calvin-mcd/universal-vault/Project/hhkb universal.kicad_sch

## KiCad design Project/hhkb universal.kicad_sch (2023-12-22)

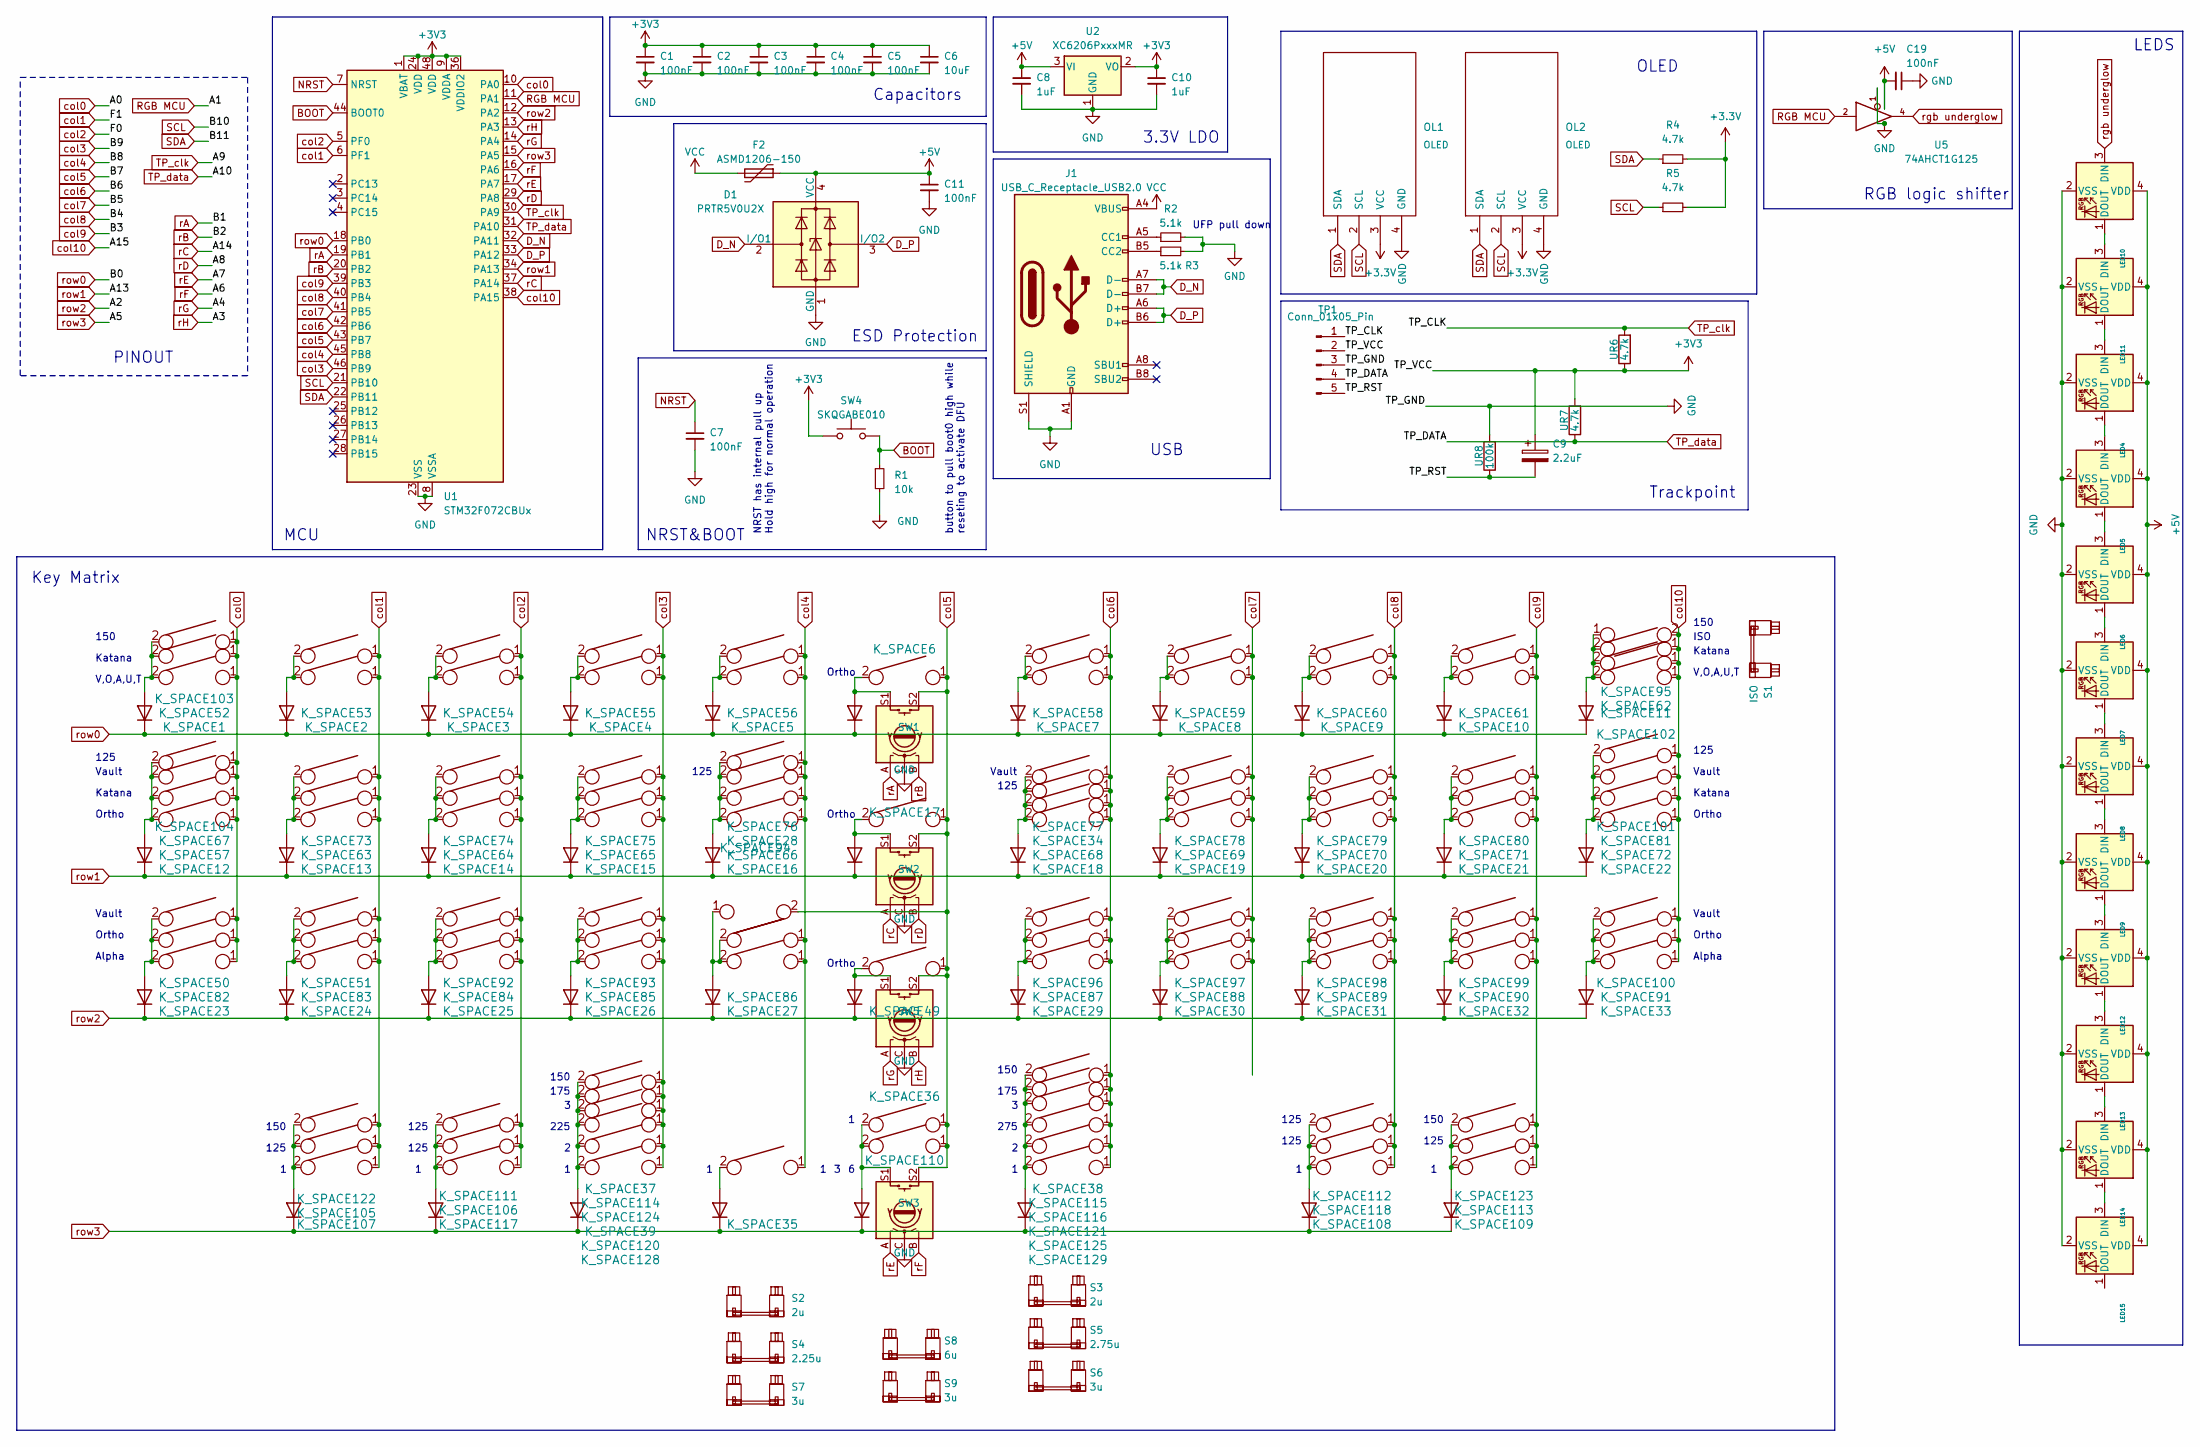
[picture p5: schematic hhkb universal.kicad_sch]

Parts:
C1, C2, C3, C4, C5, C7, C11, C19: 100nF; C_0402_1005Metric; LCSC C1525
C6: 10uF; C_0402_1005Metric; LCSC C315248
C8, C10: 1uF; C_0402_1005Metric; LCSC C14445
C9: 2.2uF; C_0805_2012Metric
D1: PRTR5V0U2X; SOT-143; LCSC C2827688
D_SPACE1, D_SPACE2, D_SPACE3, D_SPACE4, D_SPACE5, D_SPACE6, D_SPACE7, D_SPACE8, D_SPACE9, D_SPACE10, D_SPACE11, D_SPACE12, D_SPACE13, D_SPACE14, D_SPACE15, D_SPACE16, D_SPACE17, D_SPACE18, D_SPACE19, D_SPACE20, D_SPACE21, D_SPACE22, D_SPACE23, D_SPACE24, D_SPACE25, D_SPACE26, D_SPACE27, D_SPACE28, D_SPACE29, D_SPACE30, D_SPACE31, D_SPACE32, D_SPACE33, D_SPACE34, D_SPACE35, D_SPACE36, D_SPACE37, D_SPACE38, D_SPACE39, D_SPACE40, D_SPACE42: D; D_SOD-123F; LCSC C81598
F2: ASMD1206-150; Fuse_1206_3216Metric; LCSC C135341
J1: USB_C_Receptacle_USB2.0; USB_C_Receptacle_HRO_TYPE-C-31-M-12; JlcRotOffset 180
K_SPACE1, K_SPACE2, K_SPACE3, K_SPACE4, K_SPACE5, K_SPACE6, K_SPACE7, K_SPACE8, K_SPACE9, K_SPACE10, K_SPACE11, K_SPACE12, K_SPACE13, K_SPACE14, K_SPACE15, K_SPACE16, K_SPACE17, K_SPACE18, K_SPACE19, K_SPACE20, K_SPACE21, K_SPACE22, K_SPACE24, K_SPACE25, K_SPACE26, K_SPACE27, K_SPACE29, K_SPACE30, K_SPACE31, K_SPACE32, K_SPACE35, K_SPACE36, K_SPACE39, K_SPACE49, K_SPACE51, K_SPACE52, K_SPACE53, K_SPACE54, K_SPACE55, K_SPACE56, K_SPACE57, K_SPACE58, K_SPACE59, K_SPACE60, K_SPACE61, K_SPACE62, K_SPACE63, K_SPACE64, K_SPACE65, K_SPACE66, K_SPACE68, K_SPACE69, K_SPACE70, K_SPACE71, K_SPACE72, K_SPACE73, K_SPACE74, K_SPACE75, K_SPACE76, K_SPACE77, K_SPACE78, K_SPACE79, K_SPACE80, K_SPACE82, K_SPACE83, K_SPACE84, K_SPACE85, K_SPACE86, K_SPACE87, K_SPACE88, K_SPACE89, K_SPACE90, K_SPACE91, K_SPACE92, K_SPACE93, K_SPACE94, K_SPACE95, K_SPACE96, K_SPACE97, K_SPACE98, K_SPACE99, K_SPACE105, K_SPACE110, K_SPACE113, K_SPACE116, K_SPACE117, K_SPACE118, K_SPACE120, K_SPACE121, K_SPACE124, K_SPACE125, K_SPACE128, K_SPACE129: KEYSW; SW_MX_1u
K_SPACE23, K_SPACE33, K_SPACE37, K_SPACE38, K_SPACE102, K_SPACE103, K_SPACE122, K_SPACE123: KEYSW; SW_MX_1.5u
K_SPACE28, K_SPACE34, K_SPACE67, K_SPACE100, K_SPACE101, K_SPACE104, K_SPACE106, K_SPACE107, K_SPACE108, K_SPACE109, K_SPACE111, K_SPACE112: KEYSW; SW_MX_1.25u
K_SPACE50, K_SPACE81, K_SPACE114, K_SPACE115: KEYSW; SW_MX_1.75u
LED4, LED5, LED6, LED7, LED8, LED9, LED10, LED11, LED12, LED13, LED14, LED15: WS2812_2020; LED_WS2812_2020; LCSC C965555
OL1, OL2: OLED; OLED_v2
R1: 10k; R_0402_1005Metric; LCSC C25744
R2, R3: 5.1k; R_0402_1005Metric; LCSC C25905
R4, R5: 4.7k; R_0402_1005Metric; LCSC C25900
S1: ISO; STAB_MX_ISO
S2, S3: 2u; STAB_MX_2u
S4: 2.25u; STAB_MX_2.25u
S5: 2.75u; STAB_MX_2.75u
S6, S7, S9: 3u; STAB_MX_3u
S8: 6u; STAB_MX_6u
SW1, SW2, SW3, SW5: RotaryEncoder_Switch; ROT_Alps_EC11E-Switch
SW4: SKQGABE010; SW_SPST_SKQG_WithStem; LCSC C115351
TP1: Conn_01x05_Pin; PinSocket_1x05_P2.00mm_Vertical
U1: STM32F072CBUx; QFN-48-1EP_7x7mm_P0.5mm_EP5.6x5.6mm; LCSC C92504
U2: XC6206PxxxMR; SOT-23-3; LCSC C5446
U5: 74AHCT1G125; TSOT-23-5; LCSC C12494
UR6, UR7: 4.7k; R_0805_2012Metric_Pad1.20x1.40mm_HandSolder
UR8: 100k; R_0805_2012Metric_Pad1.20x1.40mm_HandSolder

Connections:
+3.3V: OL1.3 (VCC), OL2.3 (VCC), R4.2, R5.2
+3V3: C1.1, C2.1, C3.1, C4.1, C5.1, C6.1, C9.1, C10.1, SW4.1, TP1.2, U1.1 (VBAT), U1.9 (VDDA), U1.24 (VDD), U1.36 (VDDIO2), U1.48 (VDD), U2.2 (VO), UR6.1, UR7.2
+5V: C8.1, C11.1, C19.2, D1.4 (VCC), F2.1, LED4.4 (VDD), LED5.4 (VDD), LED6.4 (VDD), LED7.4 (VDD), LED8.4 (VDD), LED9.4 (VDD), LED10.4 (VDD), LED11.4 (VDD), LED12.4 (VDD), LED13.4 (VDD), LED14.4 (VDD), LED15.4 (VDD), U2.3 (VI), U5.5 (+5V)
BOOT: R1.1, SW4.2, U1.44 (BOOT0)
D_N: D1.2 (I/O1), J1.A7 (D-), J1.B7 (D-), U1.32 (PA11)
D_P: D1.3 (I/O2), J1.A6 (D+), J1.B6 (D+), U1.33 (PA12)
GND: C1.2, C2.2, C3.2, C4.2, C5.2, C6.2, C7.2, C8.2, C10.2, C11.2, C19.1, D1.1 (GND), J1.A1 (GND), J1.A12 (GND), J1.B1 (GND), J1.B12 (GND), J1.S1 (SHIELD), LED4.2 (VSS), LED5.2 (VSS), LED6.2 (VSS), LED7.2 (VSS), LED8.2 (VSS), LED9.2 (VSS), LED10.2 (VSS), LED11.2 (VSS), LED12.2 (VSS), LED13.2 (VSS), LED14.2 (VSS), LED15.2 (VSS), OL1.4 (GND), OL2.4 (GND), R1.2, R2.2, R3.2, SW1.C, SW2.C, SW3.C, SW5.C, TP1.3, U1.8 (VSSA), U1.23 (VSS), U1.35 (VSS), U1.47 (VSS), U1.49 (VSS), U2.1 (GND), U5.1, U5.3 (GND), UR8.2
NRST: C7.1, U1.7 (NRST)
unnamed: D_SPACE1.2 (A), K_SPACE1.2, K_SPACE52.2, K_SPACE103.2
unnamed: D_SPACE2.2 (A), K_SPACE2.2, K_SPACE53.2
unnamed: D_SPACE3.2 (A), K_SPACE3.2, K_SPACE54.2
unnamed: D_SPACE4.2 (A), K_SPACE4.2, K_SPACE55.2
unnamed: D_SPACE5.2 (A), K_SPACE5.2, K_SPACE56.2
unnamed: D_SPACE6.2 (A), K_SPACE6.2, SW1.S1
unnamed: D_SPACE7.2 (A), K_SPACE7.2, K_SPACE58.2
unnamed: D_SPACE8.2 (A), K_SPACE8.2, K_SPACE59.2
unnamed: D_SPACE9.2 (A), K_SPACE9.2, K_SPACE60.2
unnamed: D_SPACE10.2 (A), K_SPACE10.2, K_SPACE61.2
unnamed: D_SPACE11.2 (A), K_SPACE11.2, K_SPACE62.2, K_SPACE95.2, K_SPACE102.1
unnamed: D_SPACE12.2 (A), K_SPACE12.2, K_SPACE57.2, K_SPACE67.2, K_SPACE104.2
unnamed: D_SPACE13.2 (A), K_SPACE13.2, K_SPACE63.2, K_SPACE73.2
unnamed: D_SPACE14.2 (A), K_SPACE14.2, K_SPACE64.2, K_SPACE74.2
unnamed: D_SPACE15.2 (A), K_SPACE15.2, K_SPACE65.2, K_SPACE75.2
unnamed: D_SPACE16.2 (A), K_SPACE16.2, K_SPACE28.2, K_SPACE66.2, K_SPACE76.2
unnamed: D_SPACE17.2 (A), K_SPACE17.2, SW2.S1
unnamed: D_SPACE18.2 (A), K_SPACE18.2, K_SPACE34.2, K_SPACE68.2, K_SPACE77.2
unnamed: D_SPACE19.2 (A), K_SPACE19.2, K_SPACE69.2, K_SPACE78.2
unnamed: D_SPACE20.2 (A), K_SPACE20.2, K_SPACE70.2, K_SPACE79.2
unnamed: D_SPACE21.2 (A), K_SPACE21.2, K_SPACE71.2, K_SPACE80.2
unnamed: D_SPACE22.2 (A), K_SPACE22.2, K_SPACE72.2, K_SPACE81.2, K_SPACE101.2
unnamed: D_SPACE23.2 (A), K_SPACE23.2, K_SPACE50.2, K_SPACE82.2
unnamed: D_SPACE24.2 (A), K_SPACE24.2, K_SPACE51.2, K_SPACE83.2
unnamed: D_SPACE25.2 (A), K_SPACE25.2, K_SPACE84.2, K_SPACE92.2
unnamed: D_SPACE26.2 (A), K_SPACE26.2, K_SPACE85.2, K_SPACE93.2
unnamed: D_SPACE27.2 (A), K_SPACE27.2, K_SPACE86.2, K_SPACE94.1
unnamed: D_SPACE28.2 (A), K_SPACE49.2, SW5.S1
unnamed: D_SPACE29.2 (A), K_SPACE29.2, K_SPACE87.2, K_SPACE96.2
unnamed: D_SPACE30.2 (A), K_SPACE30.2, K_SPACE88.2, K_SPACE97.2
unnamed: D_SPACE31.2 (A), K_SPACE31.2, K_SPACE89.2, K_SPACE98.2
unnamed: D_SPACE32.2 (A), K_SPACE32.2, K_SPACE90.2, K_SPACE99.2
unnamed: D_SPACE33.2 (A), K_SPACE33.2, K_SPACE91.2, K_SPACE100.2
unnamed: D_SPACE34.2 (A), K_SPACE105.2, K_SPACE107.2, K_SPACE122.2
unnamed: D_SPACE35.2 (A), K_SPACE106.2, K_SPACE111.2, K_SPACE117.2
unnamed: D_SPACE36.2 (A), K_SPACE37.2, K_SPACE39.2, K_SPACE114.2, K_SPACE120.2, K_SPACE124.2, K_SPACE128.2
unnamed: D_SPACE37.2 (A), K_SPACE35.2
unnamed: D_SPACE38.2 (A), K_SPACE38.2, K_SPACE115.2, K_SPACE116.2, K_SPACE121.2, K_SPACE125.2, K_SPACE129.2
unnamed: D_SPACE39.2 (A), K_SPACE108.2, K_SPACE112.2, K_SPACE118.2
unnamed: D_SPACE40.2 (A), K_SPACE109.2, K_SPACE113.2, K_SPACE123.2
unnamed: D_SPACE42.2 (A), K_SPACE36.2, K_SPACE110.2, SW3.S1
unnamed: J1.A5 (CC1), R2.1
unnamed: J1.B5 (CC2), R3.1
unnamed: LED4.1 (DOUT), LED5.3 (DIN)
unnamed: LED5.1 (DOUT), LED6.3 (DIN)
unnamed: LED6.1 (DOUT), LED7.3 (DIN)
unnamed: LED7.1 (DOUT), LED8.3 (DIN)
unnamed: LED8.1 (DOUT), LED9.3 (DIN)
unnamed: LED10.1 (DOUT), LED11.3 (DIN)
unnamed: LED4.3 (DIN), LED11.1 (DOUT)
unnamed: LED12.1 (DOUT), LED13.3 (DIN)
unnamed: LED9.1 (DOUT), LED12.3 (DIN)
unnamed: LED13.1 (DOUT), LED14.3 (DIN)
unnamed: LED14.1 (DOUT), LED15.3 (DIN)
RGB MCU: U1.11 (PA1), U5.2
SCL: OL1.2 (SCL), OL2.2 (SCL), R5.1, U1.21 (PB10)
SDA: OL1.1 (SDA), OL2.1 (SDA), R4.1, U1.22 (PB11)
TP_RST: C9.2, TP1.5, UR8.1
TP_clk: TP1.1, U1.30 (PA9), UR6.2
TP_data: TP1.4, U1.31 (PA10), UR7.1
VCC: F2.2, J1.A4 (VBUS), J1.A9 (VBUS), J1.B4 (VBUS), J1.B9 (VBUS)
col0: K_SPACE1.1, K_SPACE12.1, K_SPACE23.1, K_SPACE50.1, K_SPACE52.1, K_SPACE57.1, K_SPACE67.1, K_SPACE82.1, K_SPACE103.1, K_SPACE104.1, U1.10 (PA0)
col1: K_SPACE2.1, K_SPACE13.1, K_SPACE24.1, K_SPACE51.1, K_SPACE53.1, K_SPACE63.1, K_SPACE73.1, K_SPACE83.1, K_SPACE105.1, K_SPACE107.1, K_SPACE122.1, U1.6 (PF1)
col2: K_SPACE3.1, K_SPACE14.1, K_SPACE25.1, K_SPACE54.1, K_SPACE64.1, K_SPACE74.1, K_SPACE84.1, K_SPACE92.1, K_SPACE106.1, K_SPACE111.1, K_SPACE117.1, U1.5 (PF0)
col3: K_SPACE4.1, K_SPACE15.1, K_SPACE26.1, K_SPACE37.1, K_SPACE39.1, K_SPACE55.1, K_SPACE65.1, K_SPACE75.1, K_SPACE85.1, K_SPACE93.1, K_SPACE114.1, K_SPACE120.1, K_SPACE124.1, K_SPACE128.1, U1.46 (PB9)
col4: K_SPACE5.1, K_SPACE16.1, K_SPACE27.1, K_SPACE28.1, K_SPACE35.1, K_SPACE56.1, K_SPACE66.1, K_SPACE76.1, K_SPACE86.1, U1.45 (PB8)
col5: K_SPACE6.1, K_SPACE17.1, K_SPACE36.1, K_SPACE49.1, K_SPACE94.2, K_SPACE110.1, SW1.S2, SW2.S2, SW3.S2, SW5.S2, U1.43 (PB7)
col6: K_SPACE7.1, K_SPACE18.1, K_SPACE29.1, K_SPACE34.1, K_SPACE38.1, K_SPACE58.1, K_SPACE68.1, K_SPACE77.1, K_SPACE87.1, K_SPACE96.1, K_SPACE115.1, K_SPACE116.1, K_SPACE121.1, K_SPACE125.1, K_SPACE129.1, U1.42 (PB6)
col7: K_SPACE8.1, K_SPACE19.1, K_SPACE30.1, K_SPACE59.1, K_SPACE69.1, K_SPACE78.1, K_SPACE88.1, K_SPACE97.1, U1.41 (PB5)
col8: K_SPACE9.1, K_SPACE20.1, K_SPACE31.1, K_SPACE60.1, K_SPACE70.1, K_SPACE79.1, K_SPACE89.1, K_SPACE98.1, K_SPACE108.1, K_SPACE112.1, K_SPACE118.1, U1.40 (PB4)
col9: K_SPACE10.1, K_SPACE21.1, K_SPACE32.1, K_SPACE61.1, K_SPACE71.1, K_SPACE80.1, K_SPACE90.1, K_SPACE99.1, K_SPACE109.1, K_SPACE113.1, K_SPACE123.1, U1.39 (PB3)
col10: K_SPACE11.1, K_SPACE22.1, K_SPACE33.1, K_SPACE62.1, K_SPACE72.1, K_SPACE81.1, K_SPACE91.1, K_SPACE95.1, K_SPACE100.1, K_SPACE101.1, K_SPACE102.2, U1.38 (PA15)
rA: SW1.A, U1.19 (PB1)
rB: SW1.B, U1.20 (PB2)
rC: SW2.A, U1.37 (PA14)
rD: SW2.B, U1.29 (PA8)
rE: SW3.A, U1.17 (PA7)
rF: SW3.B, U1.16 (PA6)
rG: SW5.A, U1.14 (PA4)
rH: SW5.B, U1.13 (PA3)
rgb underglow: LED10.3 (DIN), U5.4
row0: D_SPACE1.1 (K), D_SPACE2.1 (K), D_SPACE3.1 (K), D_SPACE4.1 (K), D_SPACE5.1 (K), D_SPACE6.1 (K), D_SPACE7.1 (K), D_SPACE8.1 (K), D_SPACE9.1 (K), D_SPACE10.1 (K), D_SPACE11.1 (K), U1.18 (PB0)
row1: D_SPACE12.1 (K), D_SPACE13.1 (K), D_SPACE14.1 (K), D_SPACE15.1 (K), D_SPACE16.1 (K), D_SPACE17.1 (K), D_SPACE18.1 (K), D_SPACE19.1 (K), D_SPACE20.1 (K), D_SPACE21.1 (K), D_SPACE22.1 (K), U1.34 (PA13)
row2: D_SPACE23.1 (K), D_SPACE24.1 (K), D_SPACE25.1 (K), D_SPACE26.1 (K), D_SPACE27.1 (K), D_SPACE28.1 (K), D_SPACE29.1 (K), D_SPACE30.1 (K), D_SPACE31.1 (K), D_SPACE32.1 (K), D_SPACE33.1 (K), U1.12 (PA2)
row3: D_SPACE34.1 (K), D_SPACE35.1 (K), D_SPACE36.1 (K), D_SPACE37.1 (K), D_SPACE38.1 (K), D_SPACE39.1 (K), D_SPACE40.1 (K), D_SPACE42.1 (K), U1.15 (PA5)

Notes on the sheet:
Katana
175
Ortho
125
150
150
LEDS
125
Key Matrix
Vault
NRST&BOOT
ISO
Alpha
button to pull boot0 high while reseting to activate DFU
RGB logic shifter
Trackpoint
ESD Protection
275
3.3V LDO
V,O,A,U,T
UFP pull down
USB
NRST has internal pull up Hold high for normal operation
MCU
PINOUT
OLED
Capacitors
225
